ambibayangos/150W-24V-Flyback-Converter-in-CCM/01_24V_150W_100kHz_CCM/02_Simulation/Ltspice simulation models/flyback_simplified.asc

C1: cap; 470µ
C3: cap; 66n
D1: schottky; UPSC600
D2: diode; RFN1L7S
L1: ind2; 200µ
L2: ind2; 29.8µ
M1: nmos; STP8NM60
R1: res; {RL}
R2: res; 10
R4: res; 3k
V1: voltage; PULSE(0 293 0 2m 2m 2 4)
V2: voltage; PULSE(0 12 0 50n 50n {D/f} {1/f})
Named nets: 0, vin, vds, vout
K L1 L2 0.98
.tran 0 {10m+5/f} 10m 100n
.param f=100k
.param D=0.2 RL=3.84
.meas TRAN Qg INTEG Ix(M2:G) TRIG V(n005)=50m TD=0 RISE=5 TARG V(n005)=11 TD=0 RISE=5
.MEAS TRAN Ip_rms RMS I(L1)
.MEAS TRAN Ip_peak MAX I(L1)
150W , D = 0.227, RL = 3.84
